cardonabits/haxo-hw/docs/images/haxophone001-back.png

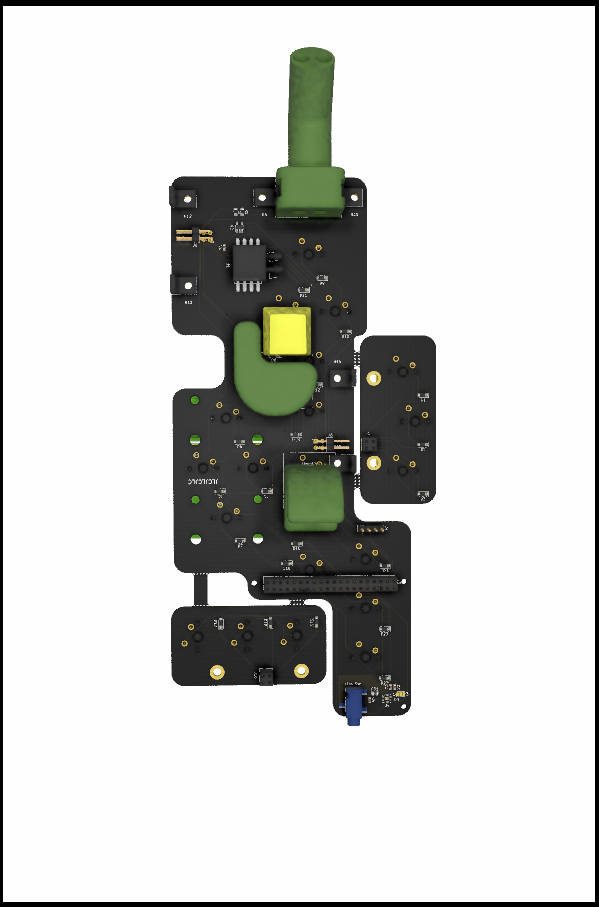
docs/images/haxophone001-back.png
