cardonabits/haxo-hw/docs/images/haxophone001-front.png

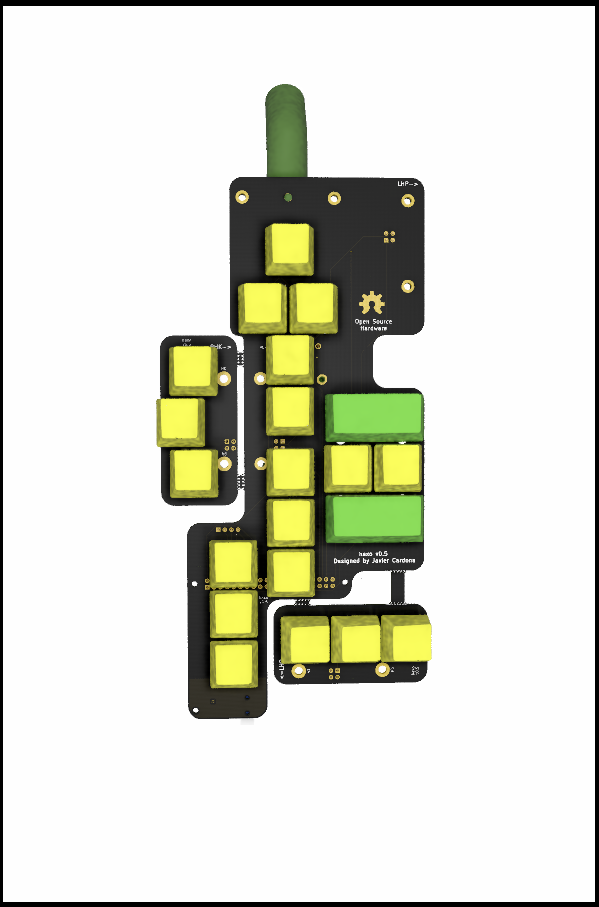
docs/images/haxophone001-front.png
