cardonabits/haxo-hw/docs/images/haxophone001-side.png

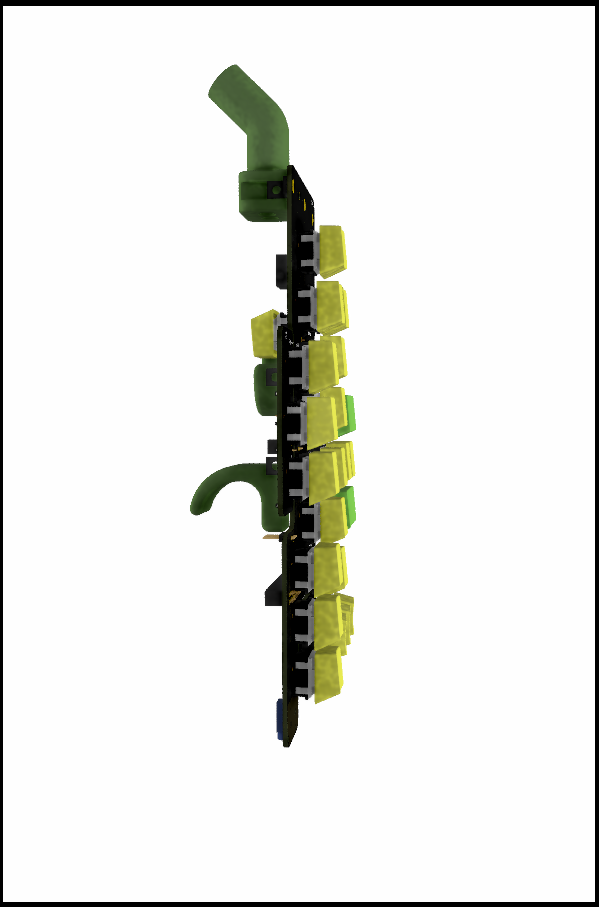
docs/images/haxophone001-side.png
