cardonabits/haxo-hw/docs/images/haxophone-4views.jpg

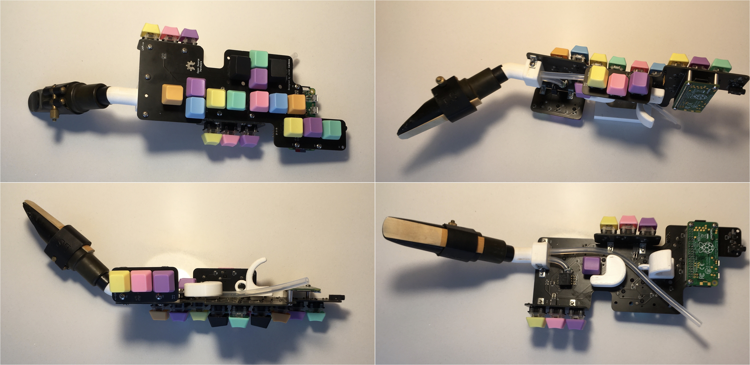
docs/images/haxophone-4views.jpg
