cardonabits/haxo-hw/docs/images/haxophone-pair.png

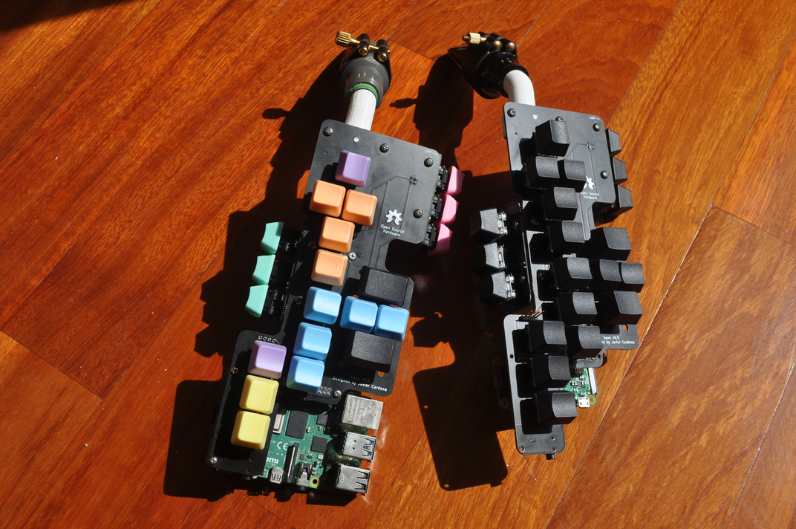
docs/images/haxophone-pair.png
