cardonabits/haxo-hw/docs/images/rpi-imager-3.png

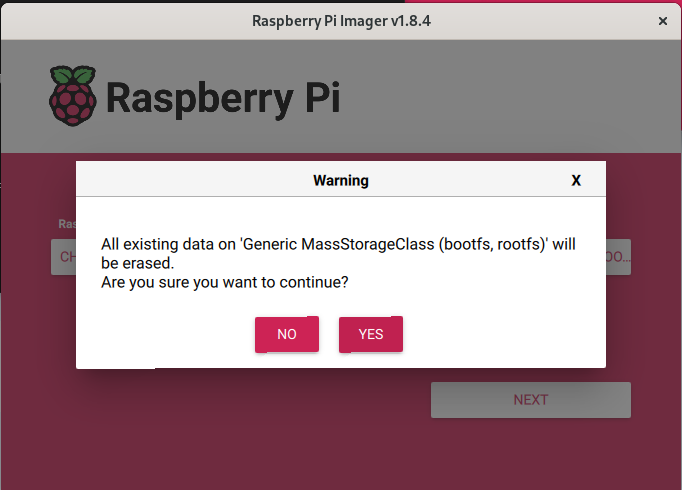
docs/images/rpi-imager-3.png
