cardonabits/haxo-hw/docs/images/vscode.png

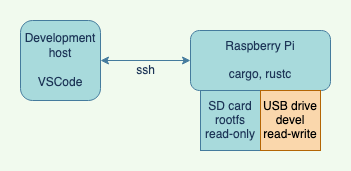
docs/images/vscode.png
