cardonabits/haxo-hw/docs/images/assembly/right_con_three.jpg

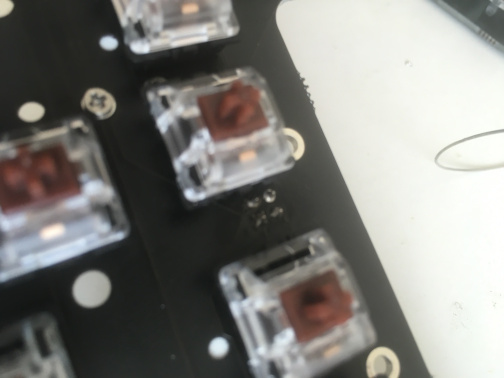
docs/images/assembly/right_con_three.jpg
