cardonabits/haxo-hw/docs/manual/cheatscheet_helper/keys/keys_commandmode_enter.png

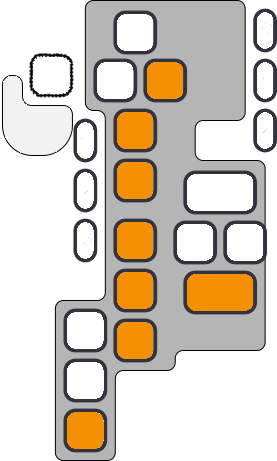
docs/manual/cheatscheet_helper/keys/keys_commandmode_enter.png
