cardonabits/haxo-hw/docs/manual/cheatscheet_helper/keys/keys_exit_mode.png

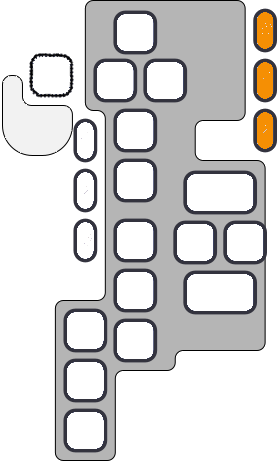
docs/manual/cheatscheet_helper/keys/keys_exit_mode.png
