cardonabits/haxo-hw/docs/manual/cheatscheet_helper/keys/keys_scroll_sounds_down_10.png

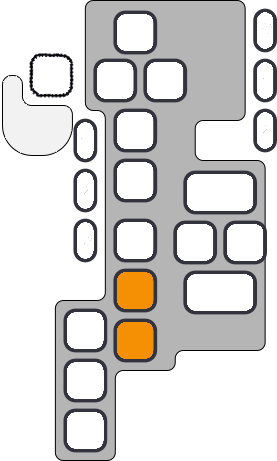
docs/manual/cheatscheet_helper/keys/keys_scroll_sounds_down_10.png
