cardonabits/haxo-hw/docs/manual/cheatscheet_helper/keys/keys_transpose_es.png

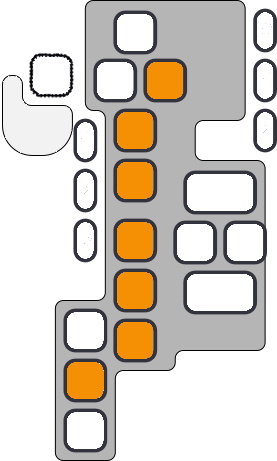
docs/manual/cheatscheet_helper/keys/keys_transpose_es.png
