cardonabits/haxo-hw/docs/manual/cheatscheet_helper/keys/keys_transpose_high_c.png

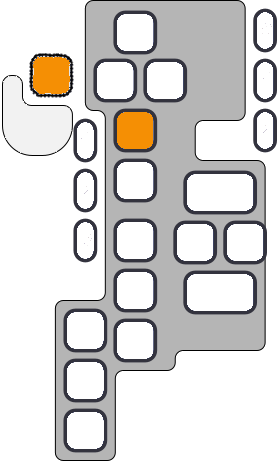
docs/manual/cheatscheet_helper/keys/keys_transpose_high_c.png
