cardonabits/haxo-hw/docs/manual/images/place_for_the_raspberry_pi.jpg

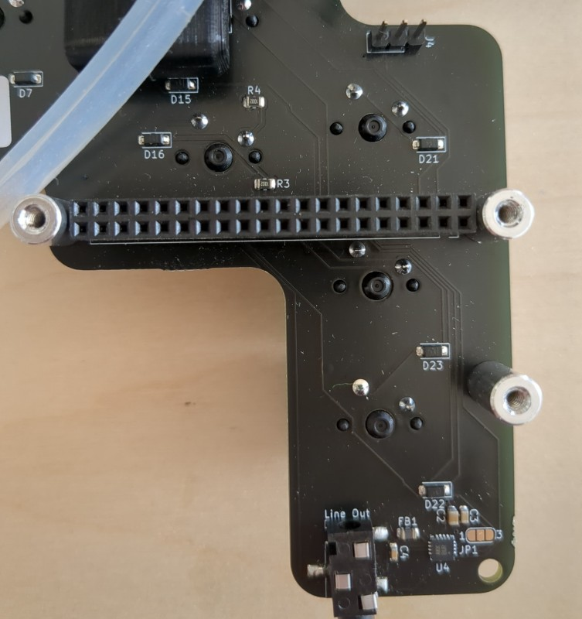
docs/manual/images/place_for_the_raspberry_pi.jpg
